ValitovTimur/spacemouse/3D/Spacemouse+V1+bbla1_stls/obj_26_magnet 2.stl

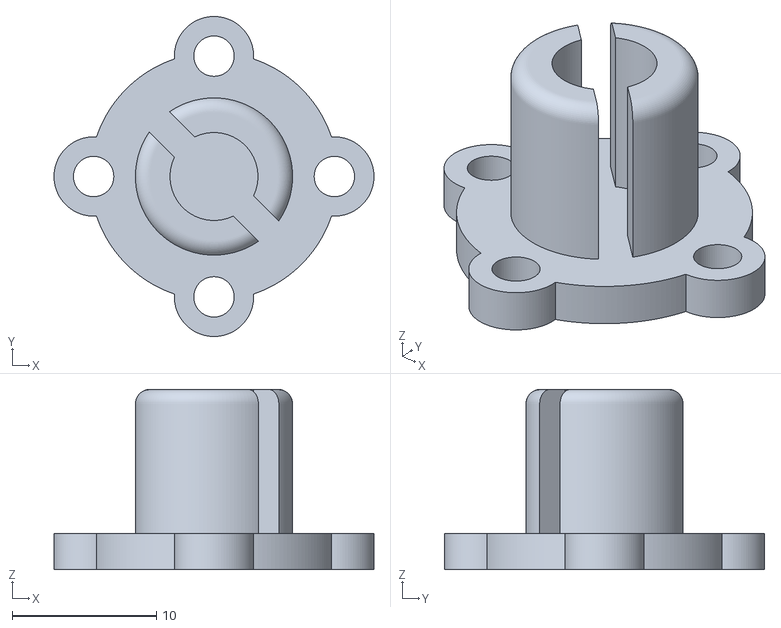
[picture p15: CAD file, 2026-03-15]
3D/Spacemouse+V1+bbla1_stls/obj_26_magnet 2.stl
22.2 x 22.2 x 12.5
