ValitovTimur/spacemouse/3D/Spacemouse+V1+bbla1_stls/obj_1_Body125.stl

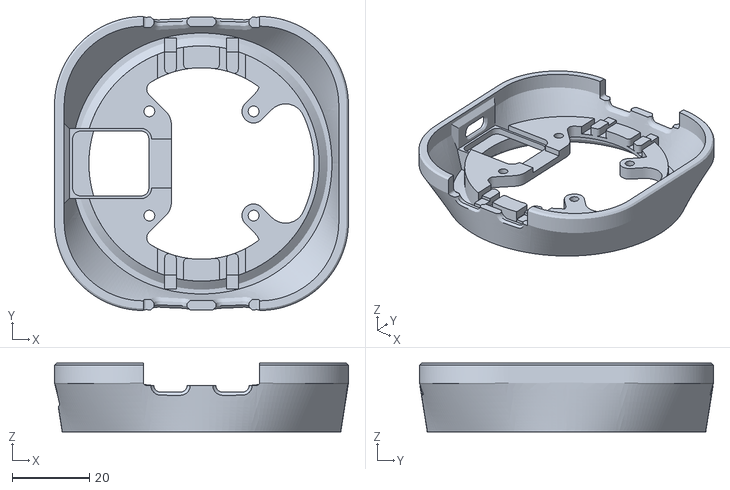
[picture p16: CAD file, 2026-03-15]
3D/Spacemouse+V1+bbla1_stls/obj_1_Body125.stl
76.0 x 76.0 x 17.8
