ValitovTimur/spacemouse/3D/Spacemouse+V1+bbla1_stls/obj_17_high base.stl

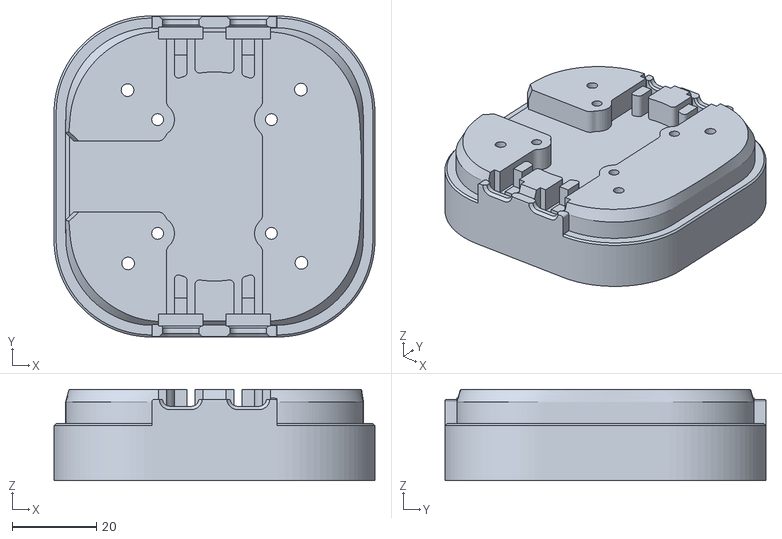
[picture p17: CAD file, 2026-03-15]
3D/Spacemouse+V1+bbla1_stls/obj_17_high base.stl
76.0 x 76.0 x 21.6
