ValitovTimur/spacemouse/3D/Spacemouse+V1+bbla1_stls/obj_15_BASE NO.stl

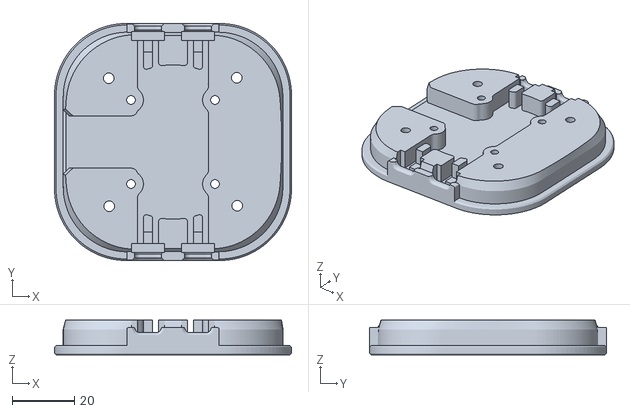
[picture p18: CAD file, 2026-03-15]
3D/Spacemouse+V1+bbla1_stls/obj_15_BASE NO.stl
76.0 x 76.0 x 11.1
