ValitovTimur/spacemouse/3D/Spacemouse+V1+bbla1_stls/obj_19_internal structure.stl

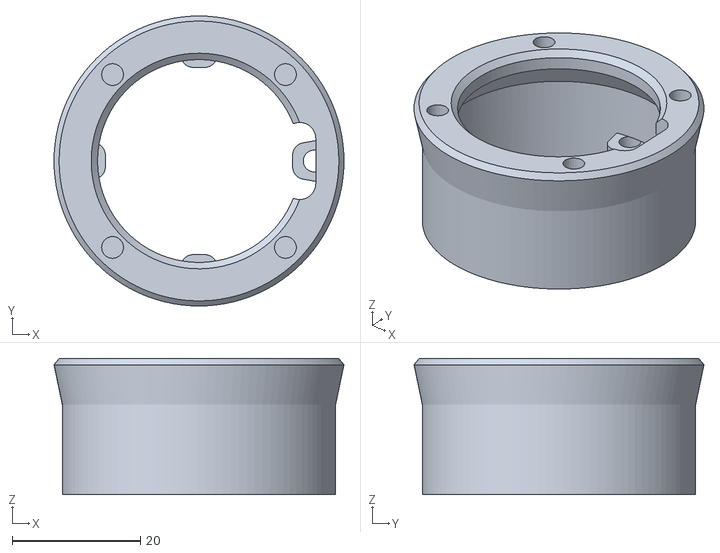
[picture p19: CAD file, 2026-03-15]
3D/Spacemouse+V1+bbla1_stls/obj_19_internal structure.stl
45.2 x 45.2 x 21.2
