ValitovTimur/spacemouse/3D/Spacemouse+V1+bbla1_stls/obj_20_hard spring.stl

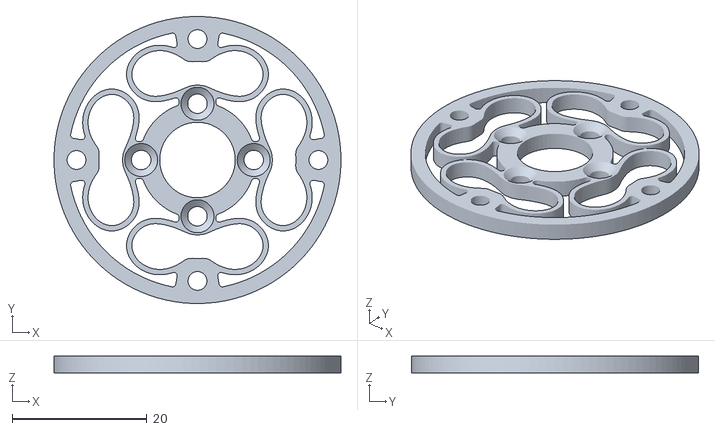
[picture p20: CAD file, 2026-03-15]
3D/Spacemouse+V1+bbla1_stls/obj_20_hard spring.stl
42.6 x 42.6 x 2.50
