ValitovTimur/spacemouse/3D/Spacemouse+V1+bbla1_stls/obj_14_standard base.stl

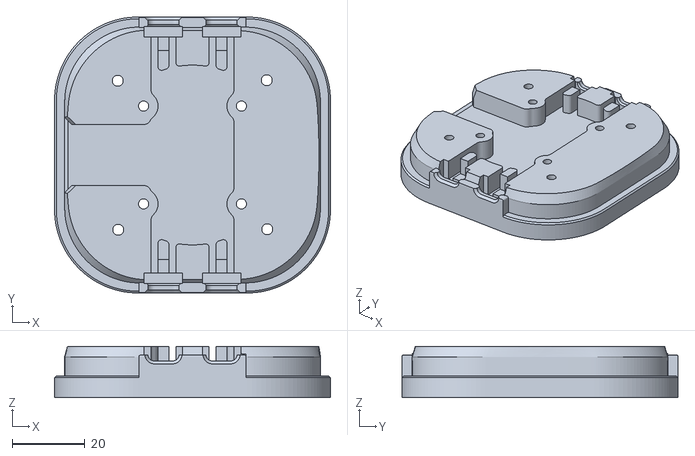
[picture p21: CAD file, 2026-03-15]
3D/Spacemouse+V1+bbla1_stls/obj_14_standard base.stl
76.0 x 76.0 x 14.1
