ValitovTimur/spacemouse/3D/Spacemouse+V1+bbla1_stls/obj_27_magnet 3.stl

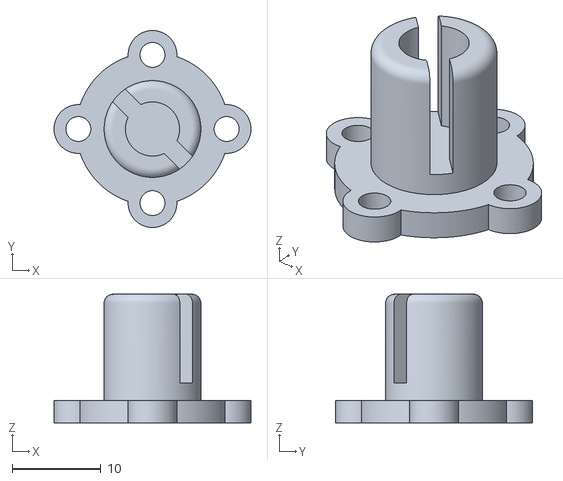
[picture p22: CAD file, 2026-03-15]
3D/Spacemouse+V1+bbla1_stls/obj_27_magnet 3.stl
22.2 x 22.2 x 14.5
