ValitovTimur/spacemouse/3D/Spacemouse+V1+bbla1_stls/obj_21_soft spring.stl

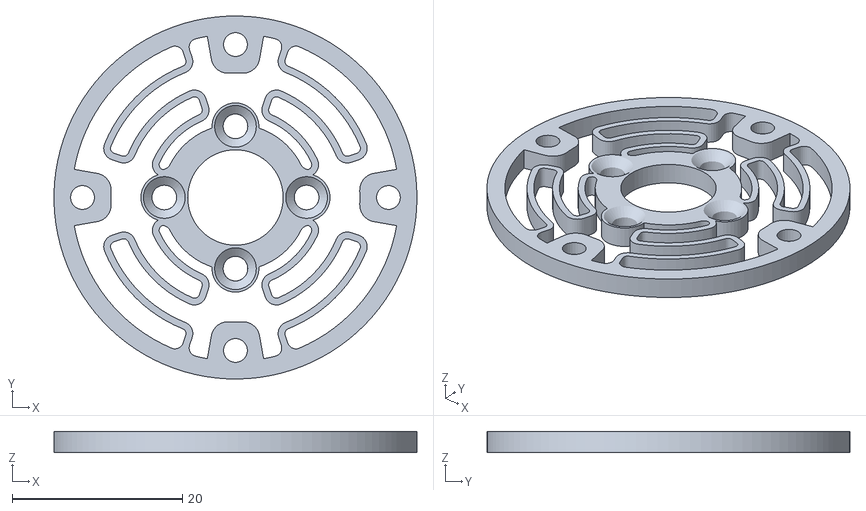
[picture p23: CAD file, 2026-03-15]
3D/Spacemouse+V1+bbla1_stls/obj_21_soft spring.stl
42.6 x 42.6 x 2.50
